paulvee/VBA-Curve-Tracer/Back Panel/BP-2DBOTRev2b.JPG

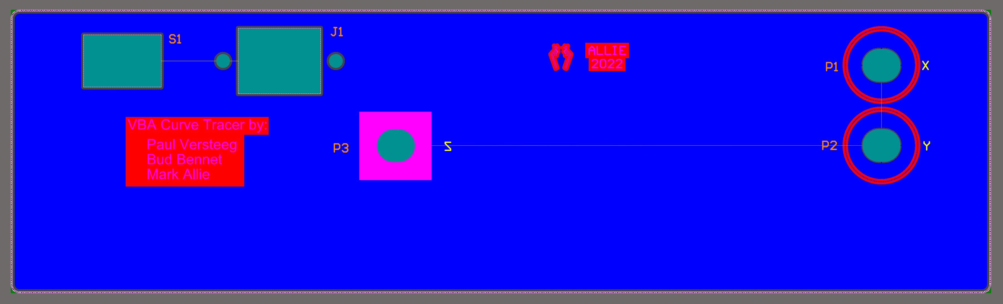
Back Panel/BP-2DBOTRev2b.JPG
