paulvee/VBA-Curve-Tracer/Back Panel/BP-2DTOPRev2b.JPG

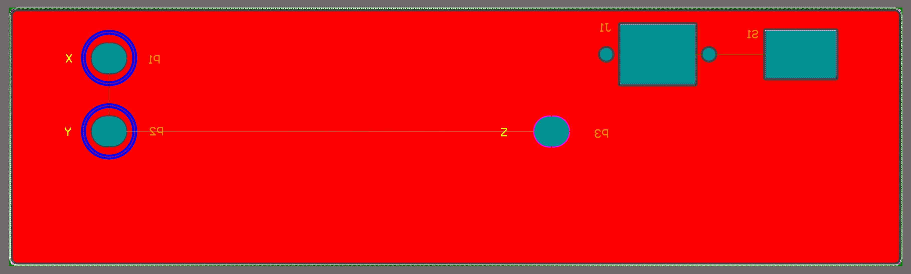
Back Panel/BP-2DTOPRev2b.JPG
