paulvee/VBA-Curve-Tracer/Back Panel/BP-3DBOTRev2b.JPG

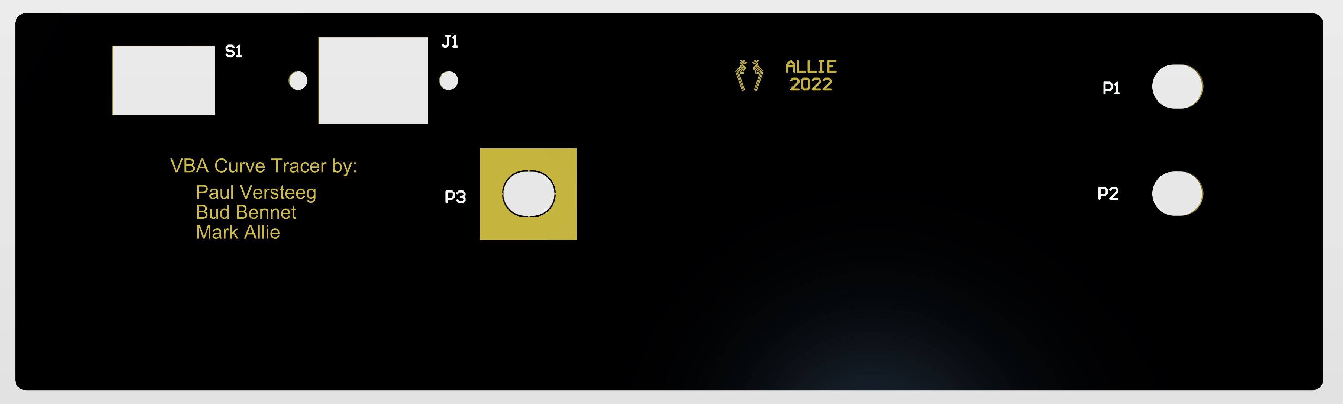
Back Panel/BP-3DBOTRev2b.JPG
