paulvee/VBA-Curve-Tracer/Back Panel/BP-3DTOPRev2b.JPG

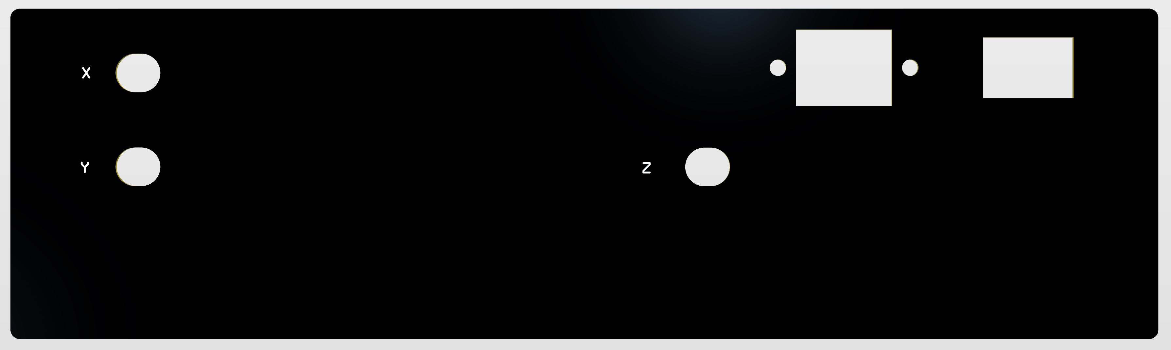
Back Panel/BP-3DTOPRev2b.JPG
