paulvee/VBA-Curve-Tracer/CT plus DSO-sm.jpg

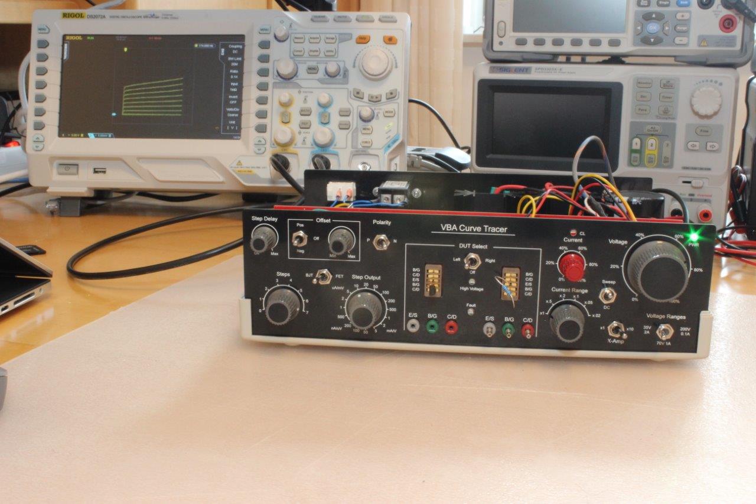
CT plus DSO-sm.jpg
