paulvee/VBA-Curve-Tracer/Front Above.jpg

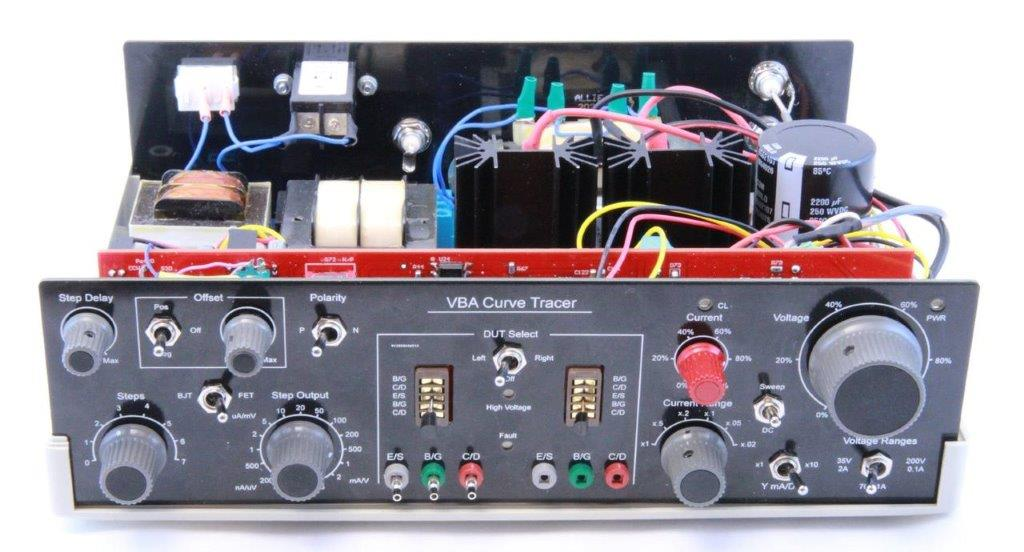
Front Above.jpg
