paulvee/VBA-Curve-Tracer/Front Board/CurrentAndVoltageSet-Rev2b.png

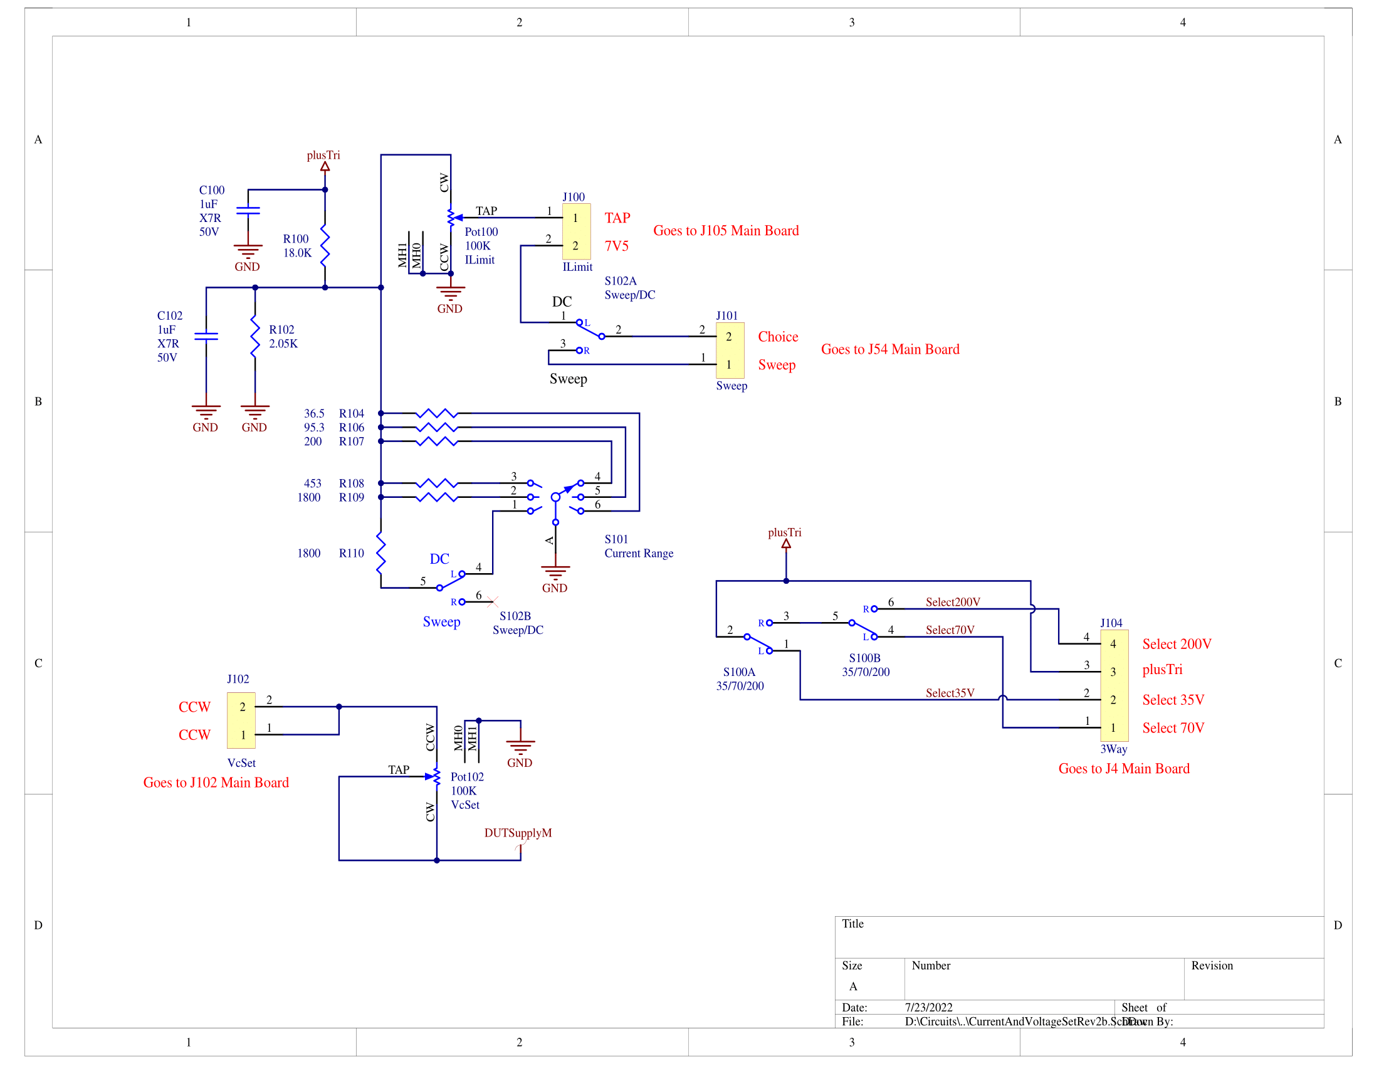
Front Board/CurrentAndVoltageSet-Rev2b.png
