paulvee/VBA-Curve-Tracer/Front Board/D2A-Rev2b.png

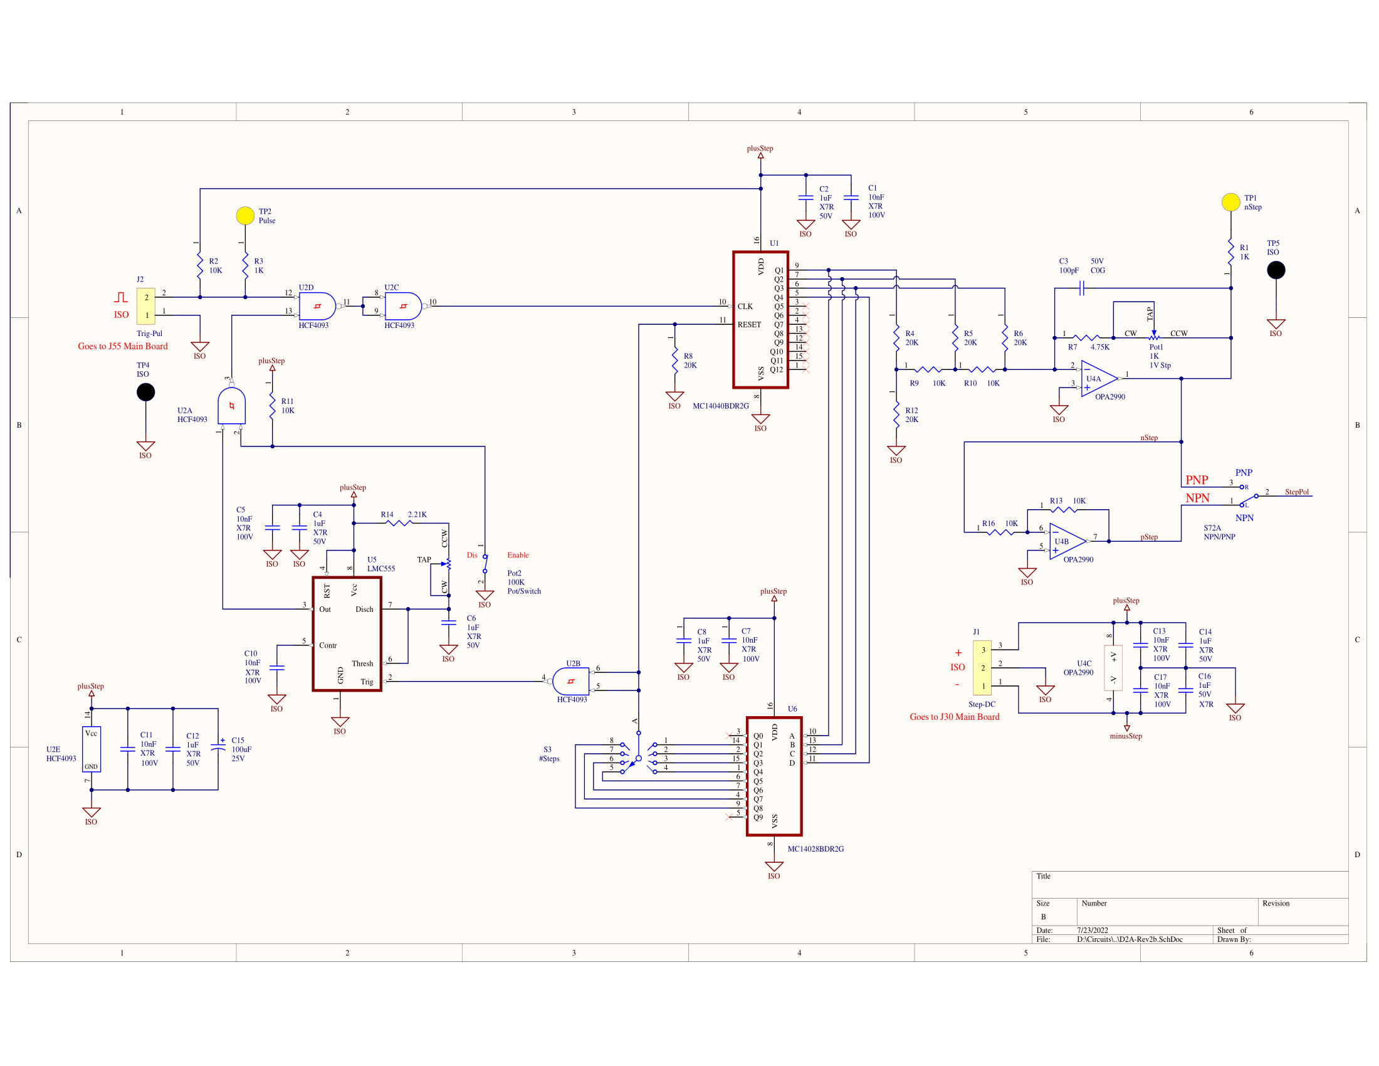
Front Board/D2A-Rev2b.png
