paulvee/VBA-Curve-Tracer/Front Board/FaultDetect-Rev2b.png

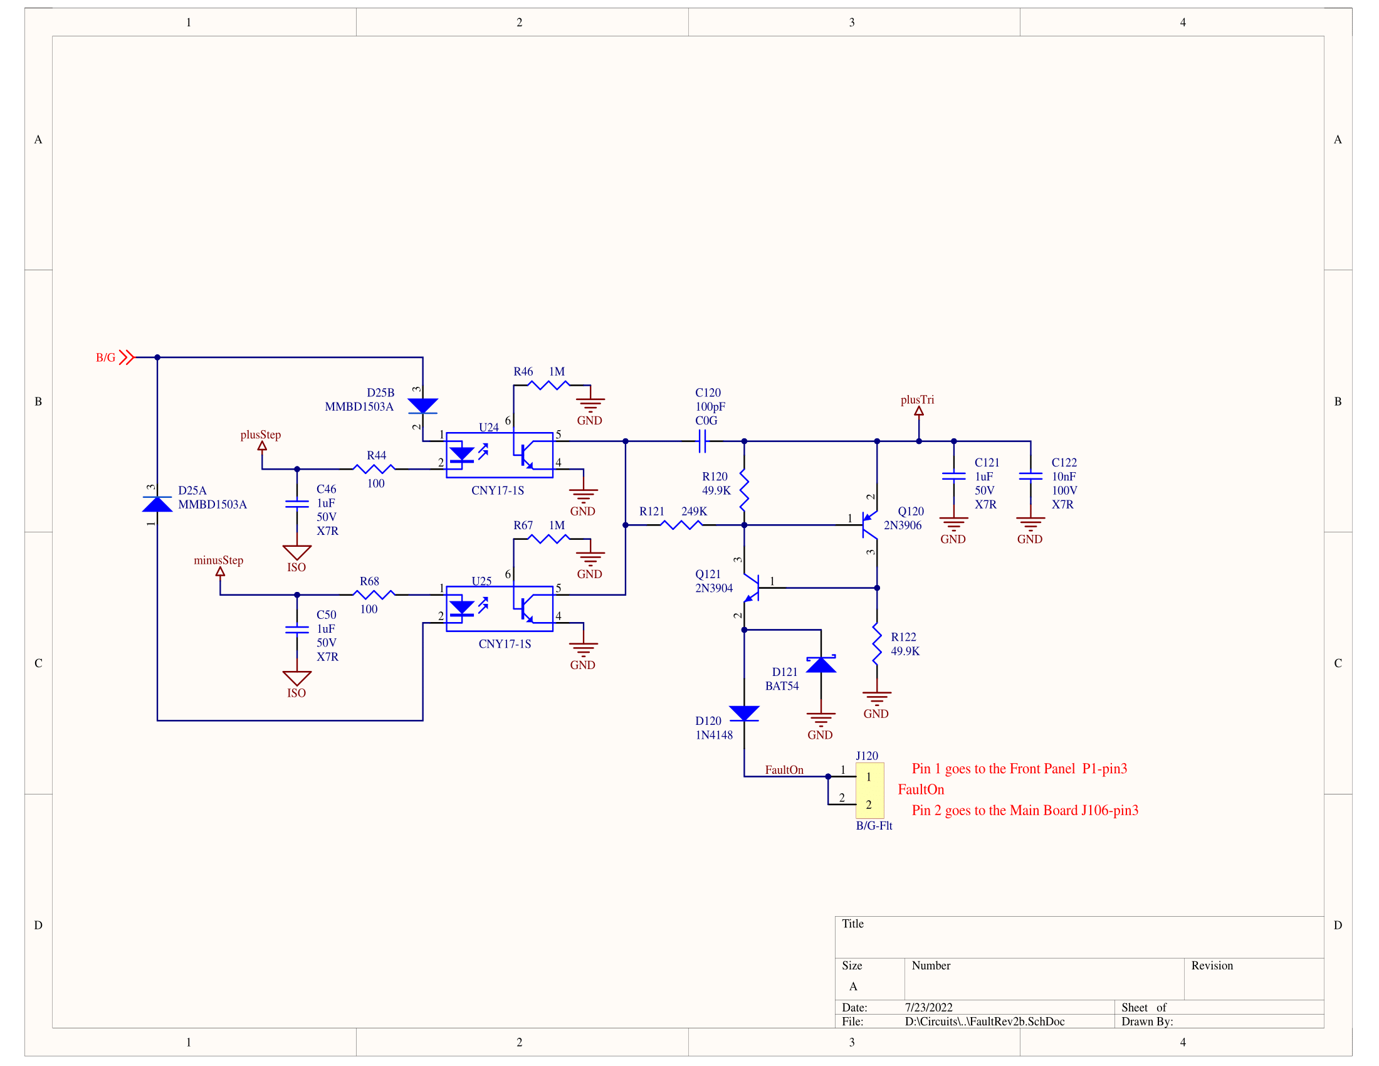
Front Board/FaultDetect-Rev2b.png
