paulvee/VBA-Curve-Tracer/Front Board/FB-2D-BOT-NoGND-NoISO-Rev2b.JPG

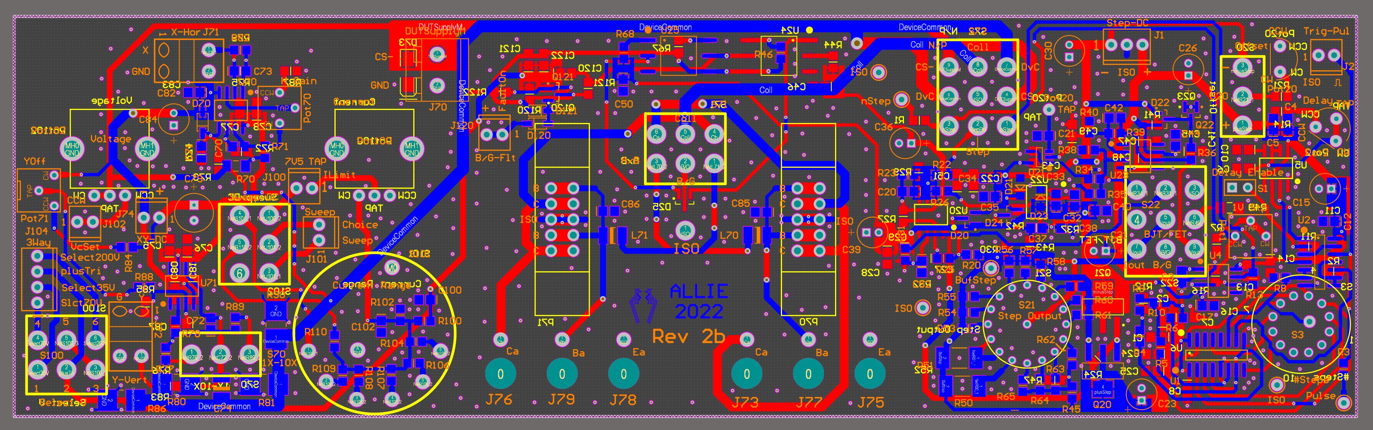
Front Board/FB-2D-BOT-NoGND-NoISO-Rev2b.JPG
