paulvee/VBA-Curve-Tracer/Front Board/FB-2D-TOP-NoGND-NoISO-Rev2b.JPG

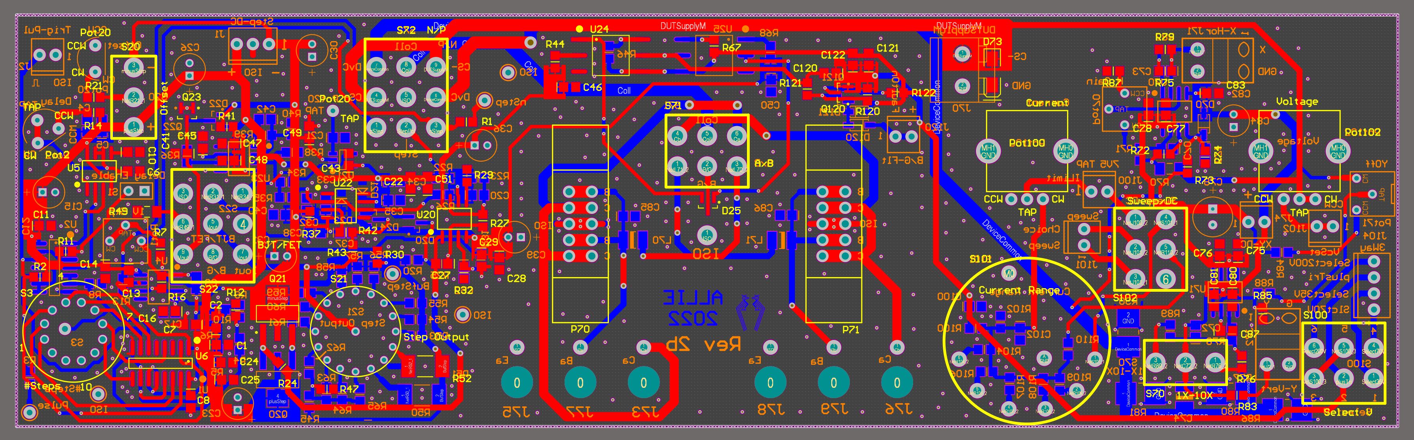
Front Board/FB-2D-TOP-NoGND-NoISO-Rev2b.JPG
