paulvee/VBA-Curve-Tracer/Front Board/FB-3D-BOT-Rev2b.png

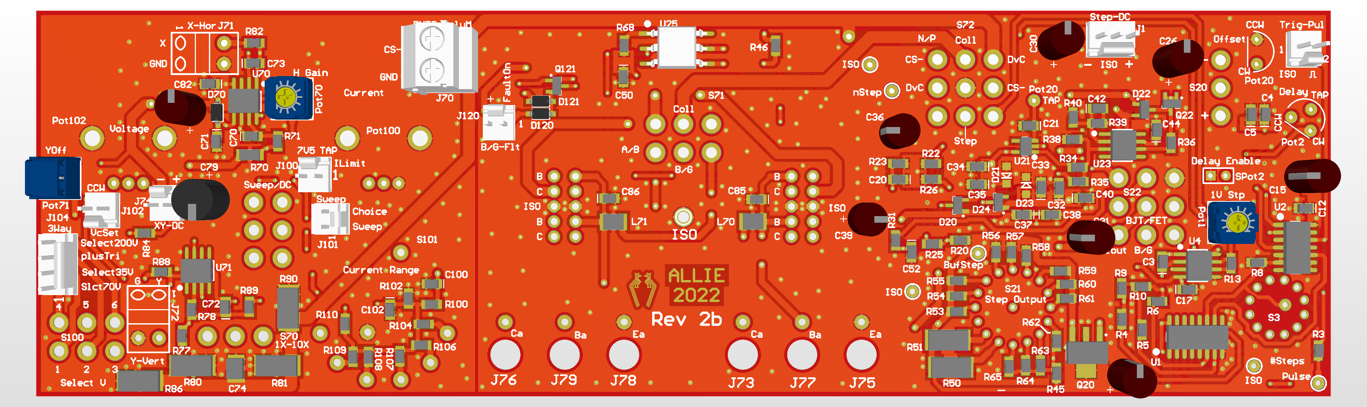
Front Board/FB-3D-BOT-Rev2b.png
