paulvee/VBA-Curve-Tracer/Front Board/FB-3D-TOP-Rev2b.png

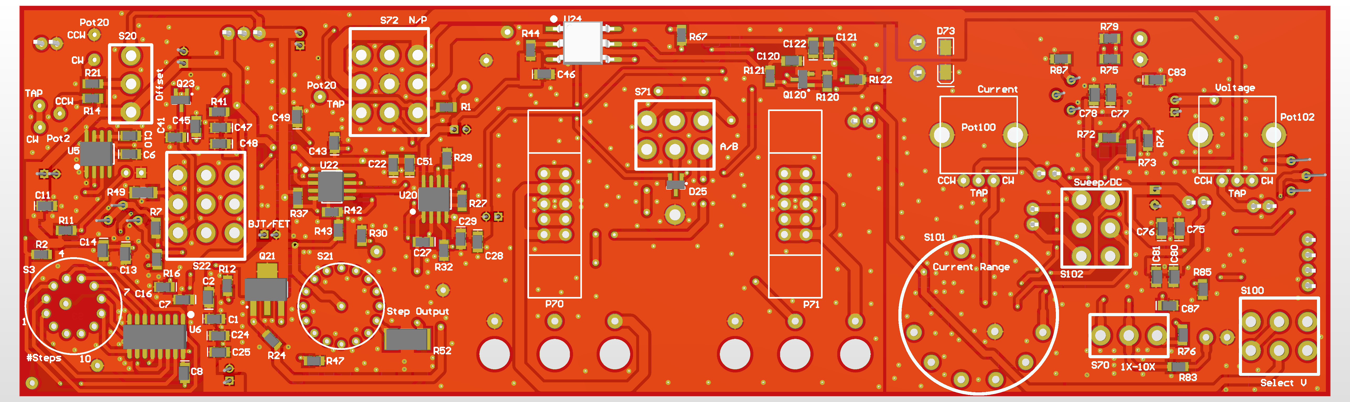
Front Board/FB-3D-TOP-Rev2b.png
