paulvee/VBA-Curve-Tracer/Front Board/XYAmp-Rev2b.png

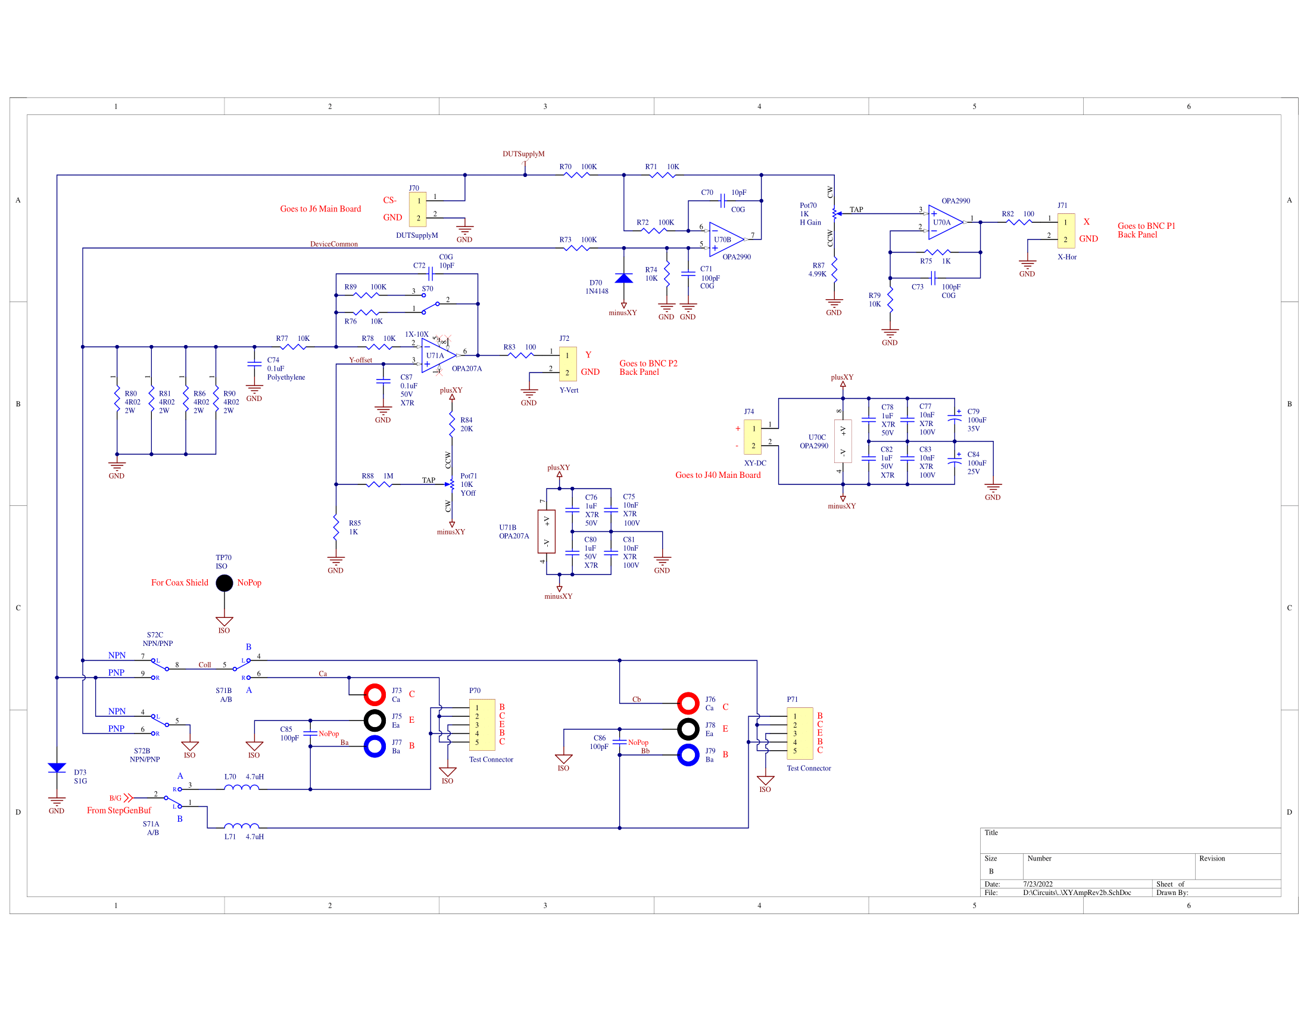
Front Board/XYAmp-Rev2b.png
