paulvee/VBA-Curve-Tracer/Front Panel/CT_Boxed(small).jpg

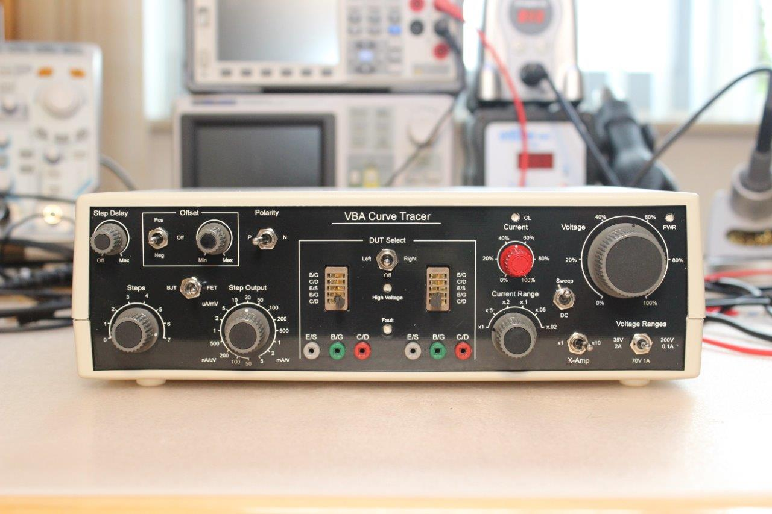
Front Panel/CT_Boxed(small).jpg
