paulvee/VBA-Curve-Tracer/Front Panel/FP-2D-BOT-Rev2b.png

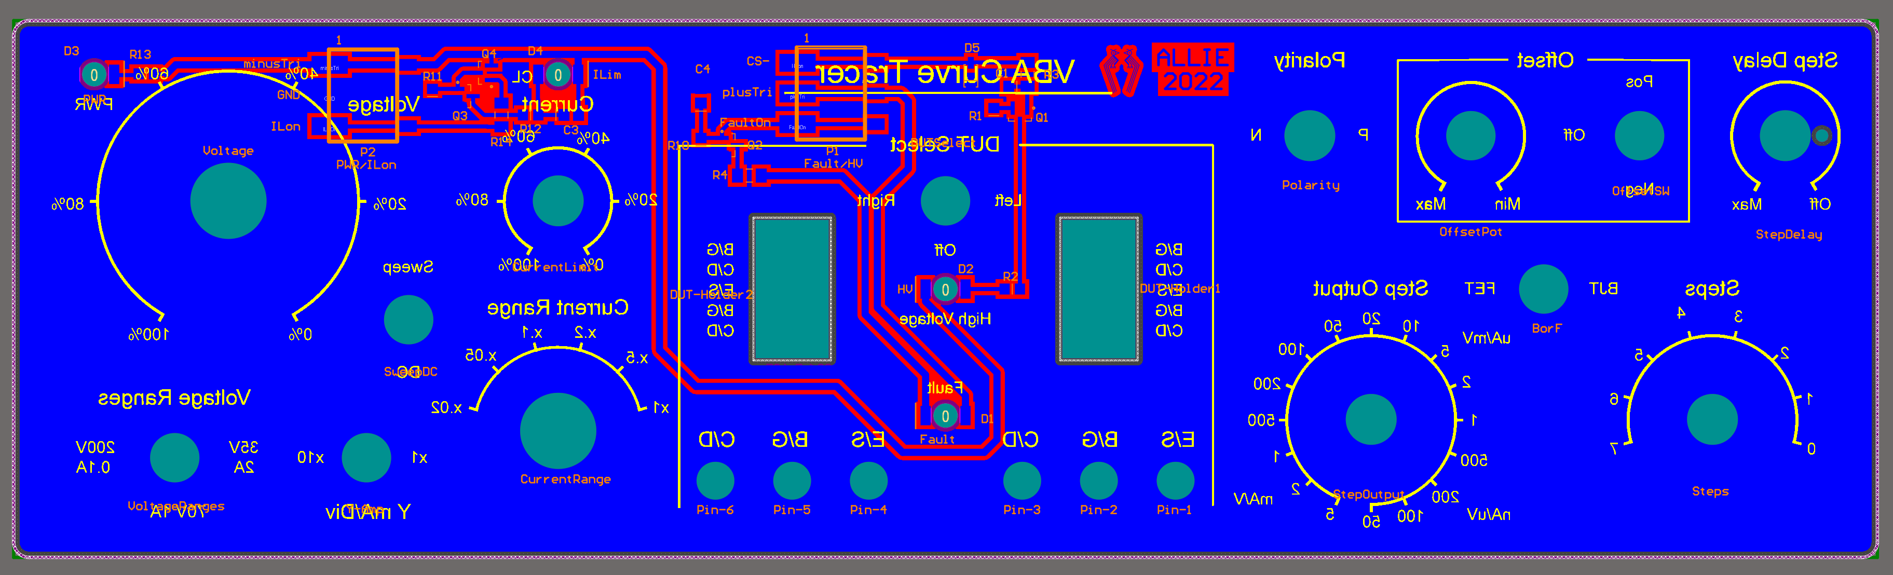
Front Panel/FP-2D-BOT-Rev2b.png
