paulvee/VBA-Curve-Tracer/Front Panel/FP-2D-TOP-Rev2b.png

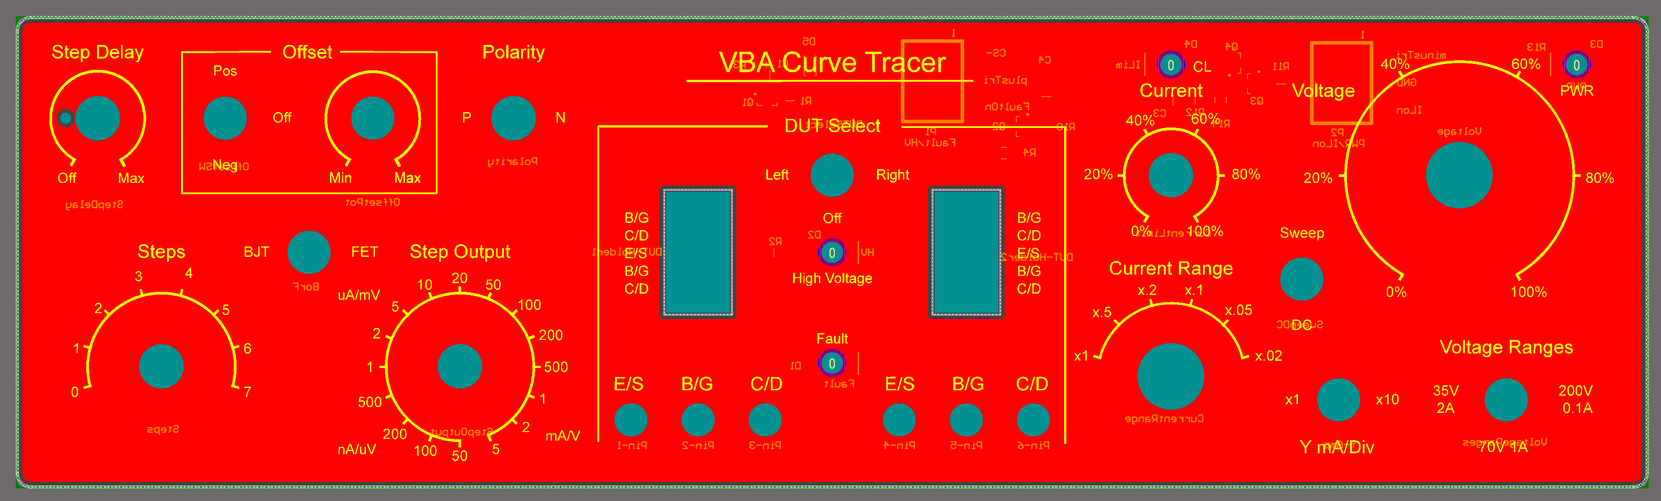
Front Panel/FP-2D-TOP-Rev2b.png
