paulvee/VBA-Curve-Tracer/Front Panel/FP-3D-BOT-Rev2b.png

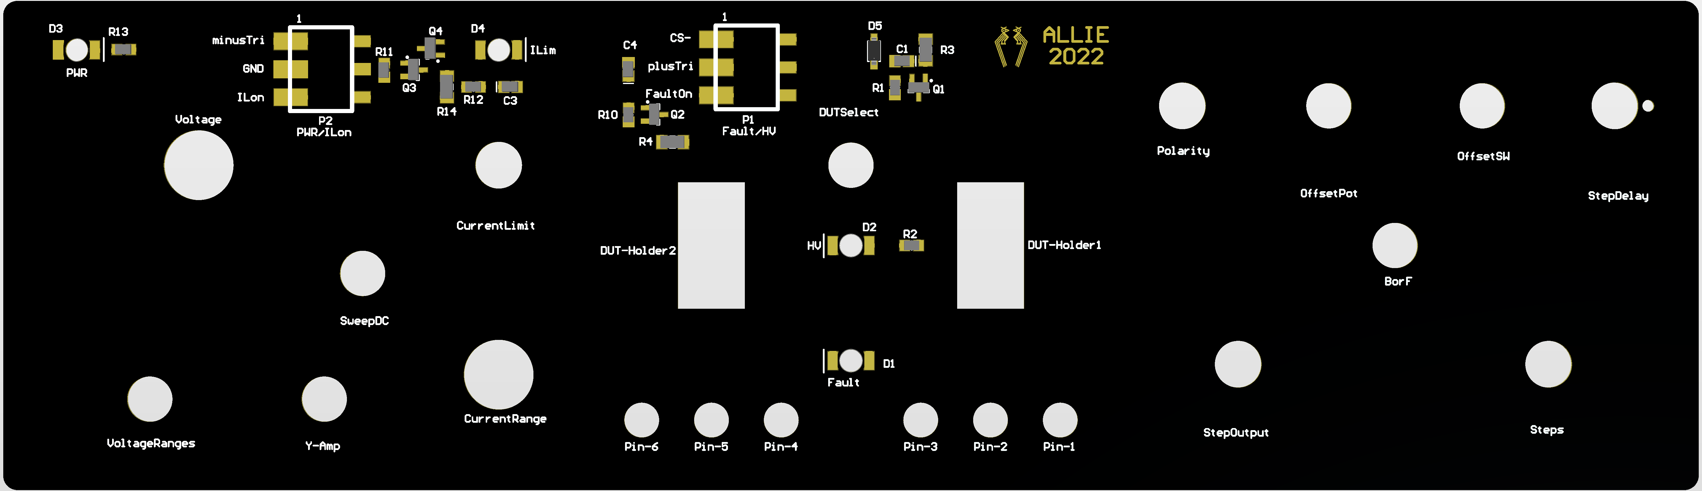
Front Panel/FP-3D-BOT-Rev2b.png
