paulvee/VBA-Curve-Tracer/Front Panel/FP-3D-TOP-Rev2b.png

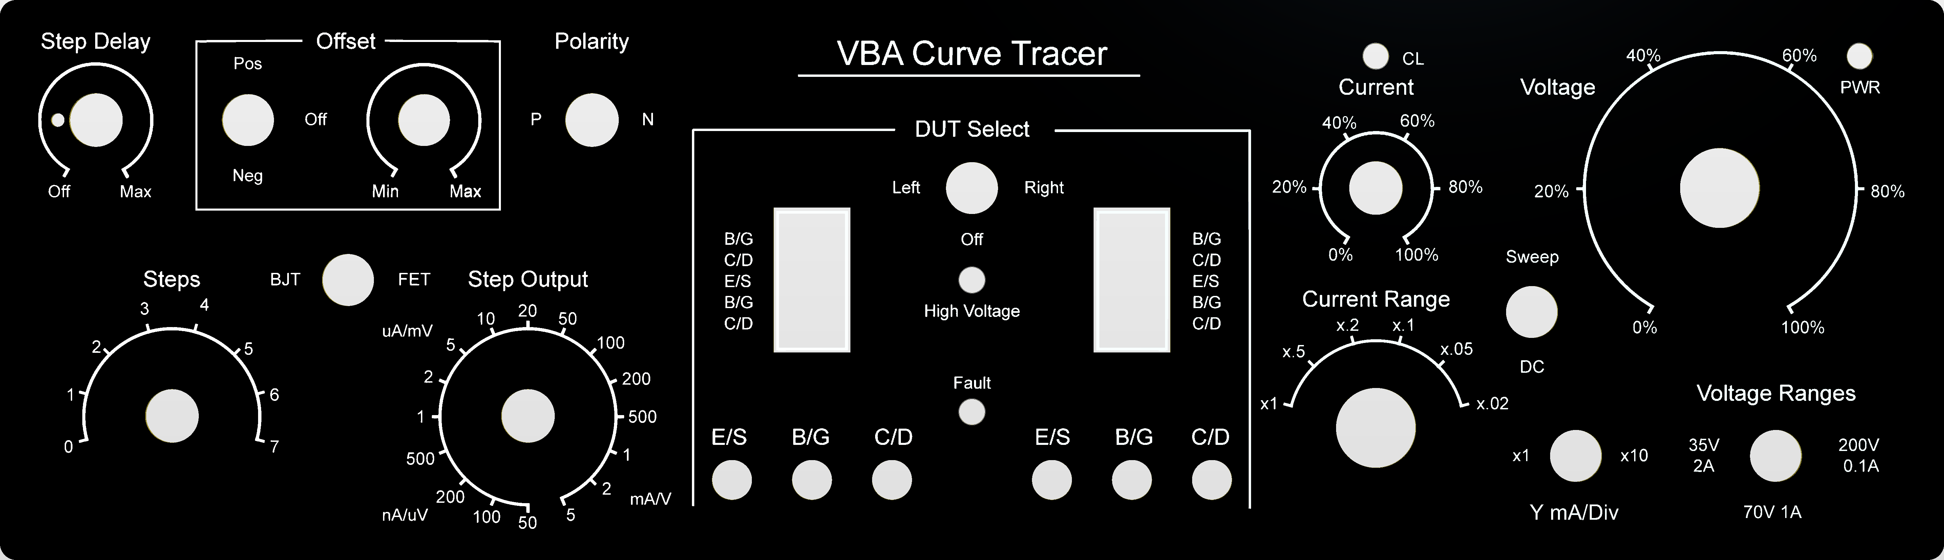
Front Panel/FP-3D-TOP-Rev2b.png
