paulvee/VBA-Curve-Tracer/Front Panel/FrontPanel-Rev2b.png

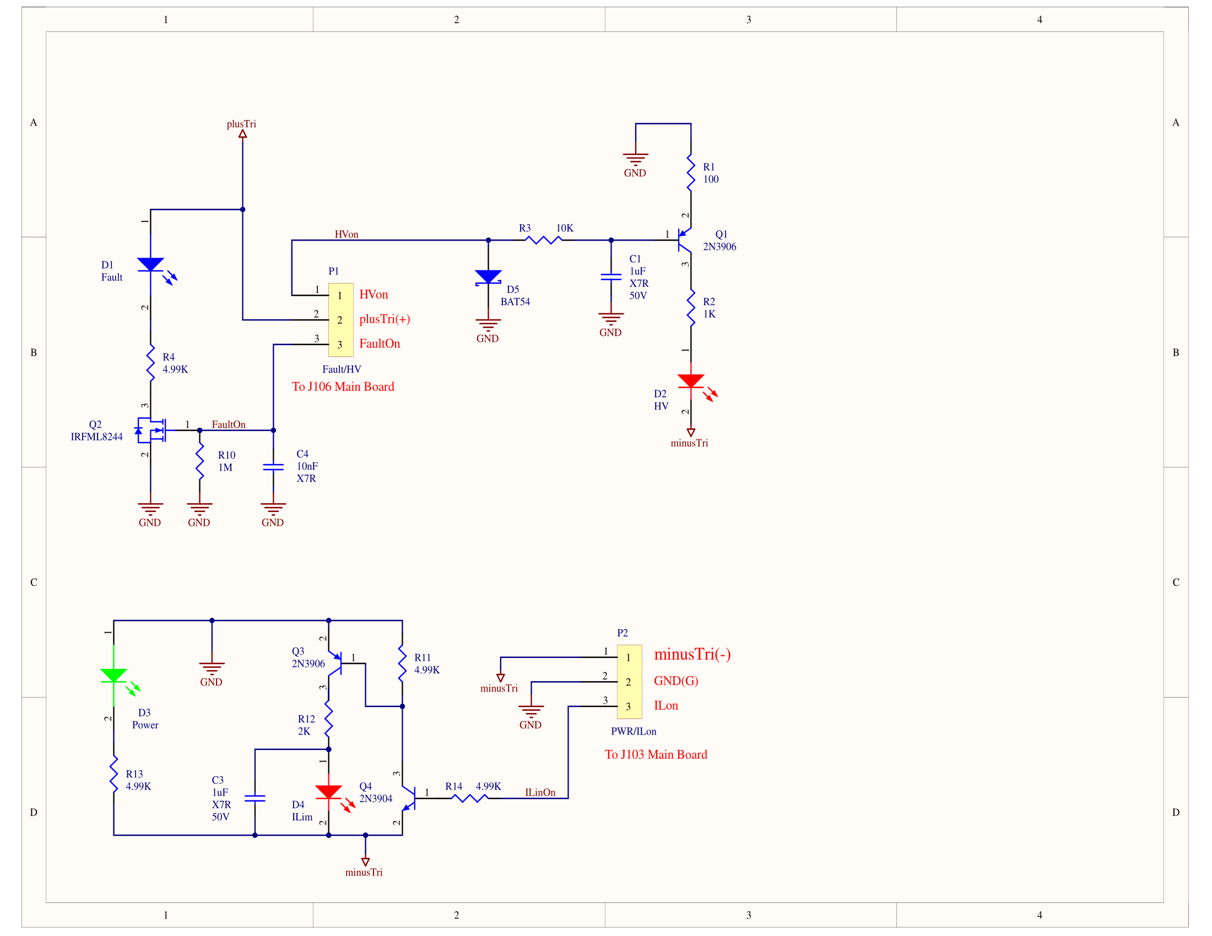
Front Panel/FrontPanel-Rev2b.png
