paulvee/VBA-Curve-Tracer/Front Panel/MountingHoles-Rev2b.png

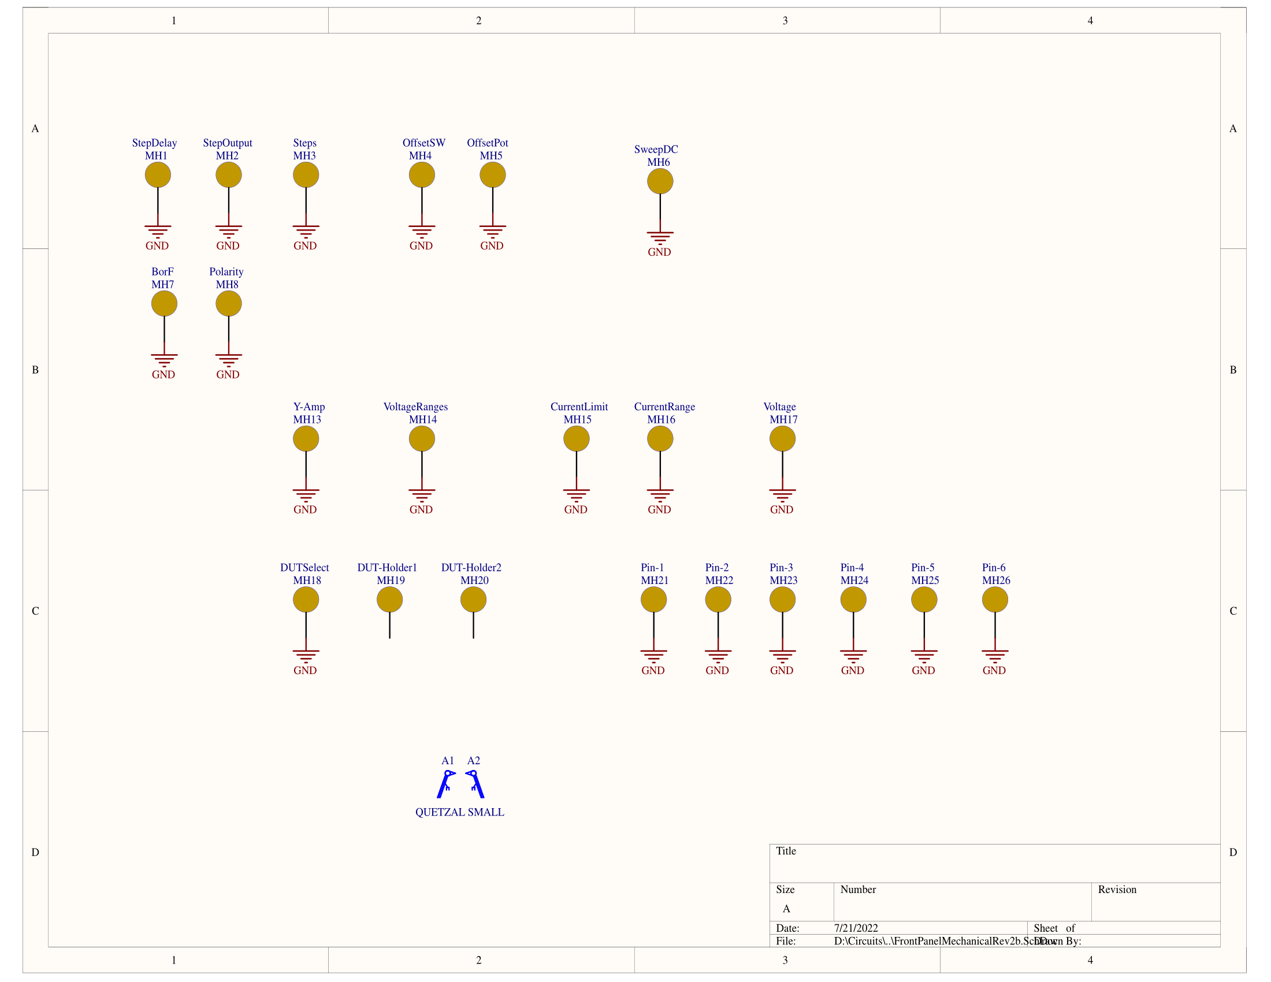
Front Panel/MountingHoles-Rev2b.png
