paulvee/VBA-Curve-Tracer/Front Panel/VBA-CT-Mark.jpg

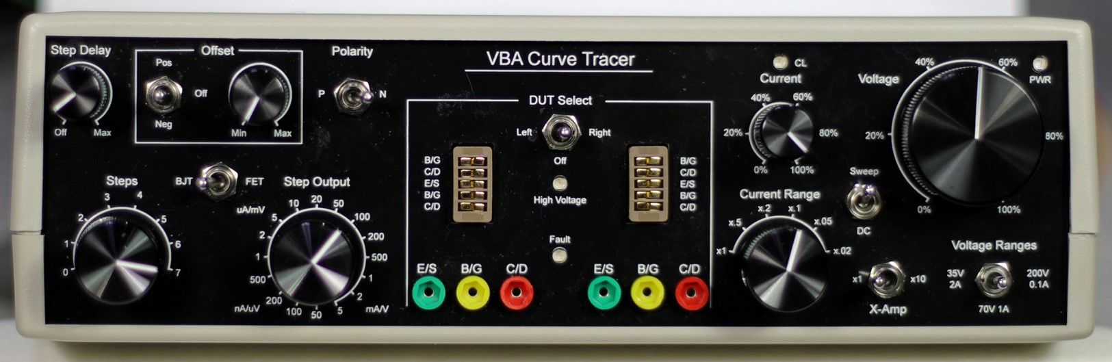
Front Panel/VBA-CT-Mark.jpg
