paulvee/VBA-Curve-Tracer/Main Board/ACSupply-Rev2b.png

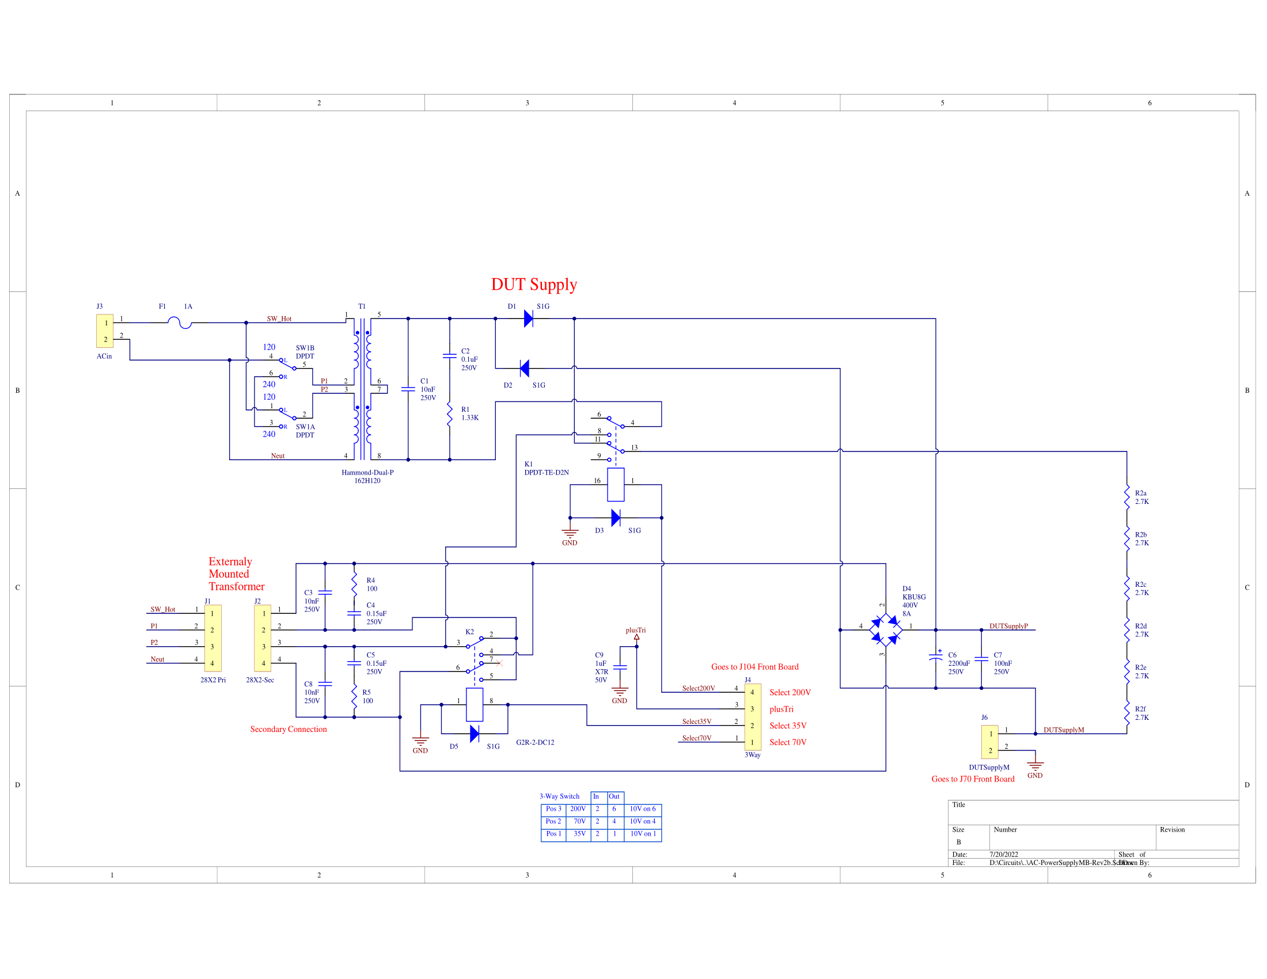
Main Board/ACSupply-Rev2b.png
