paulvee/VBA-Curve-Tracer/Main Board/CurrentSource-Rev2b.png

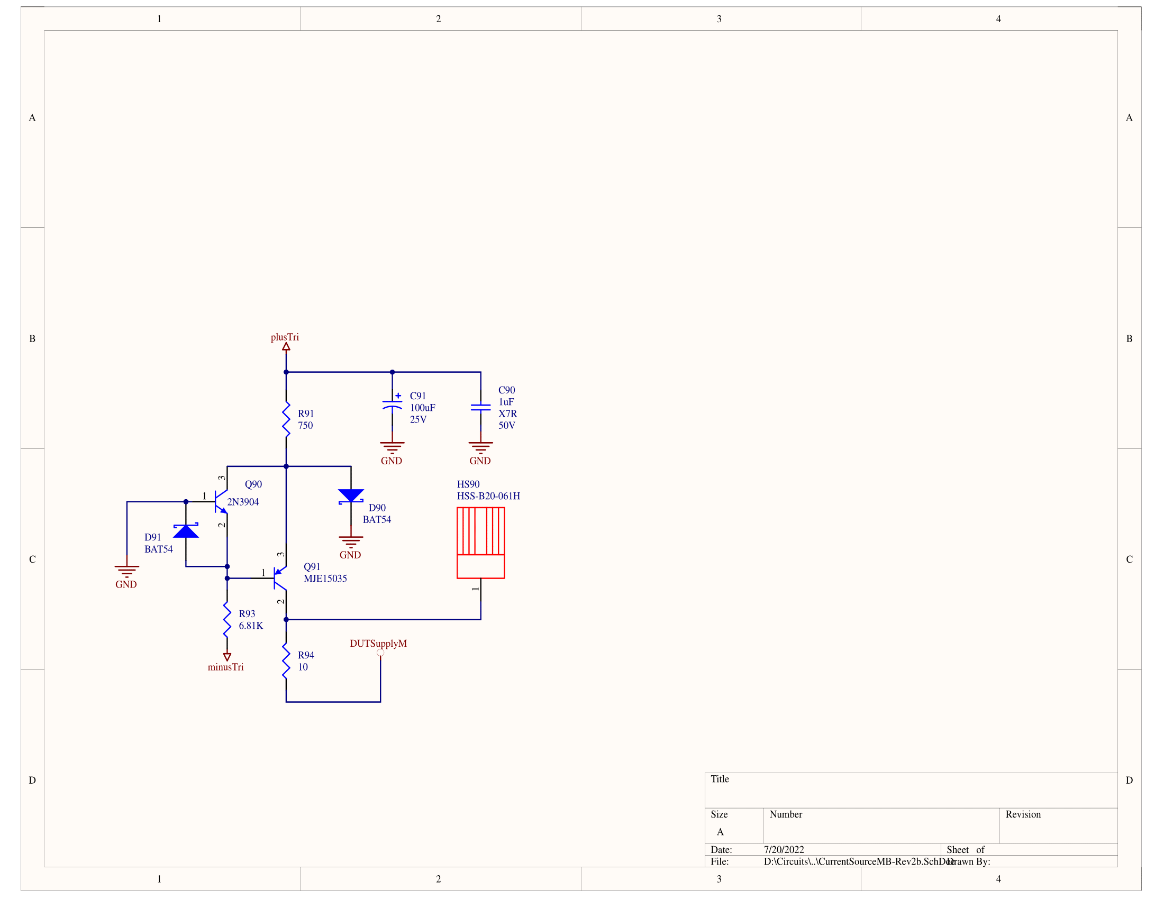
Main Board/CurrentSource-Rev2b.png
