paulvee/VBA-Curve-Tracer/Main Board/DUTSupply-Rev2b.png

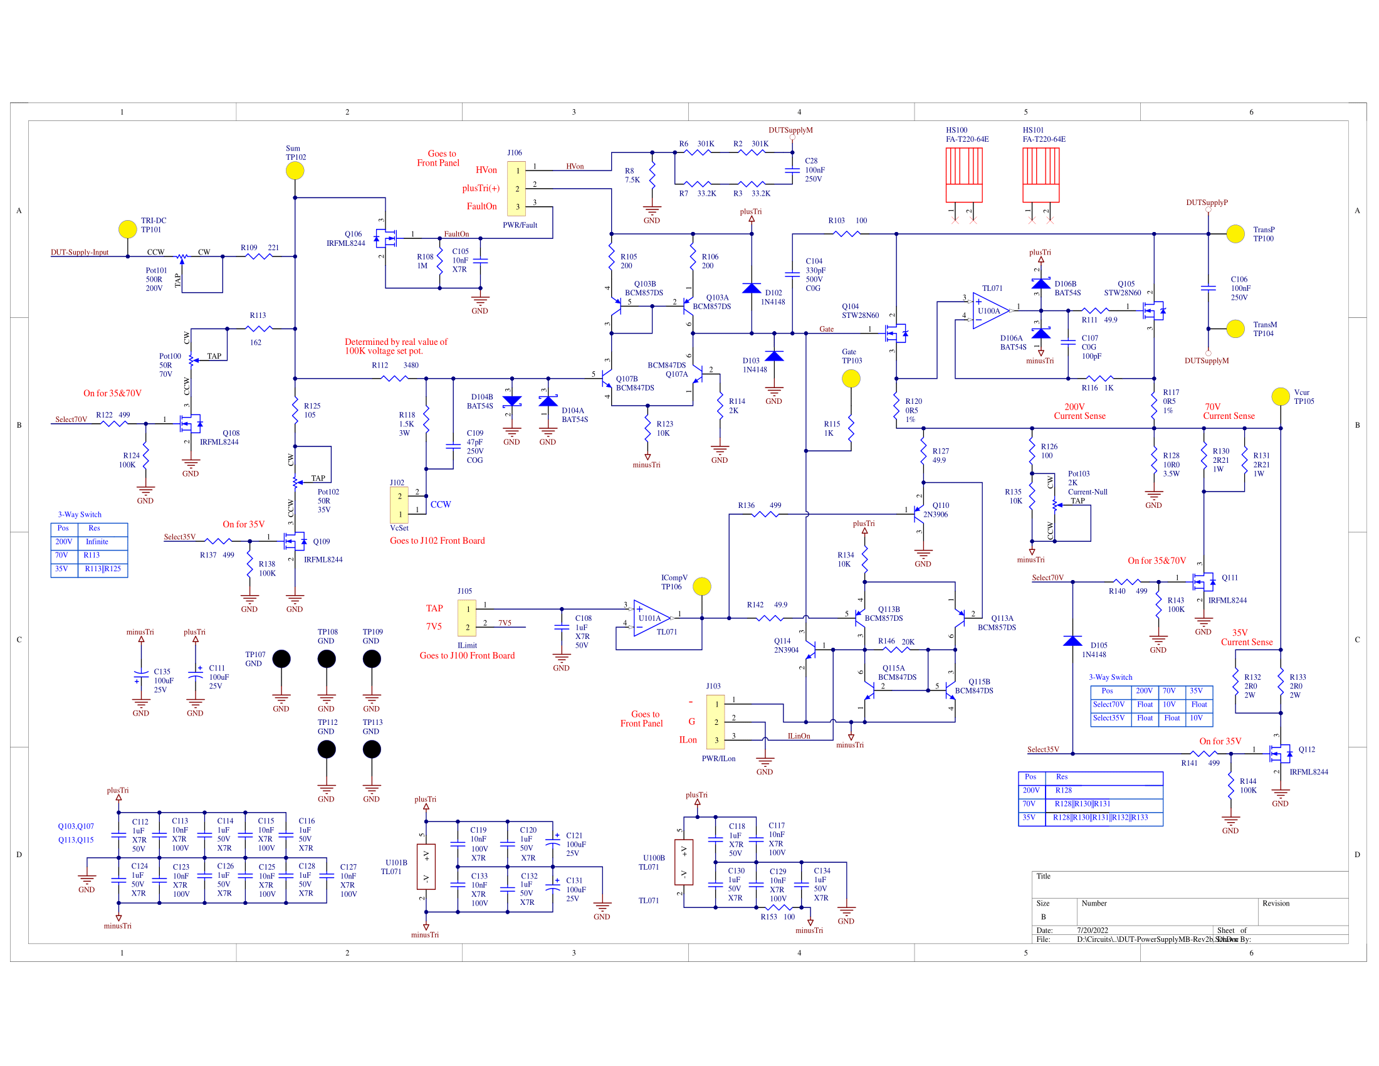
Main Board/DUTSupply-Rev2b.png
