paulvee/VBA-Curve-Tracer/Main Board/IsolatedSupply-Rev2b.png

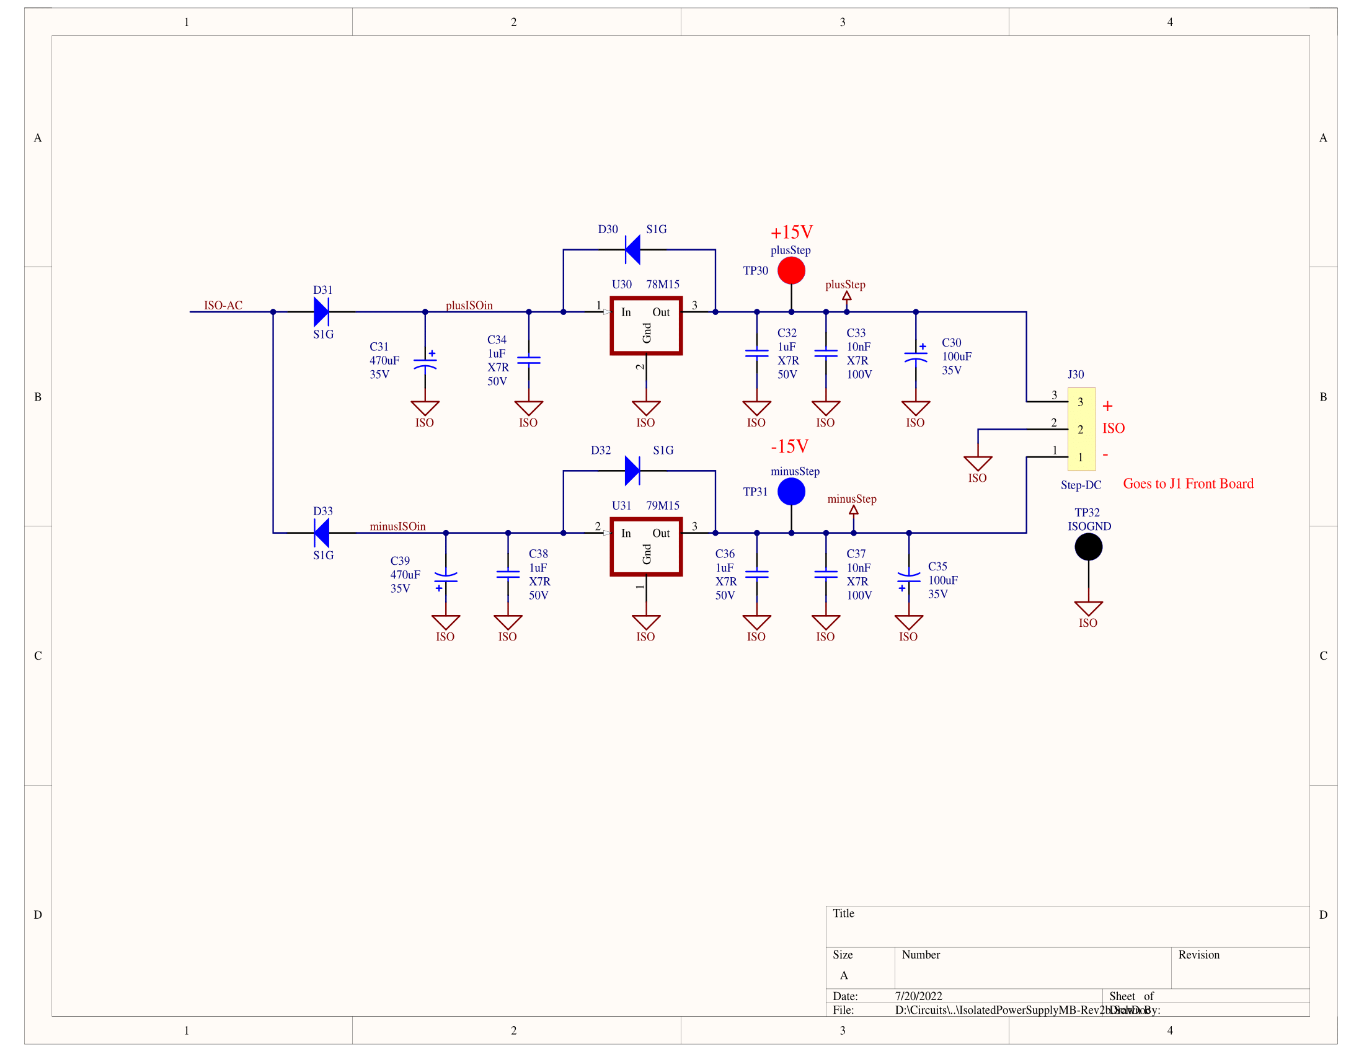
Main Board/IsolatedSupply-Rev2b.png
