paulvee/VBA-Curve-Tracer/Main Board/MB-2D-NoGND-BOTRev2b.JPG

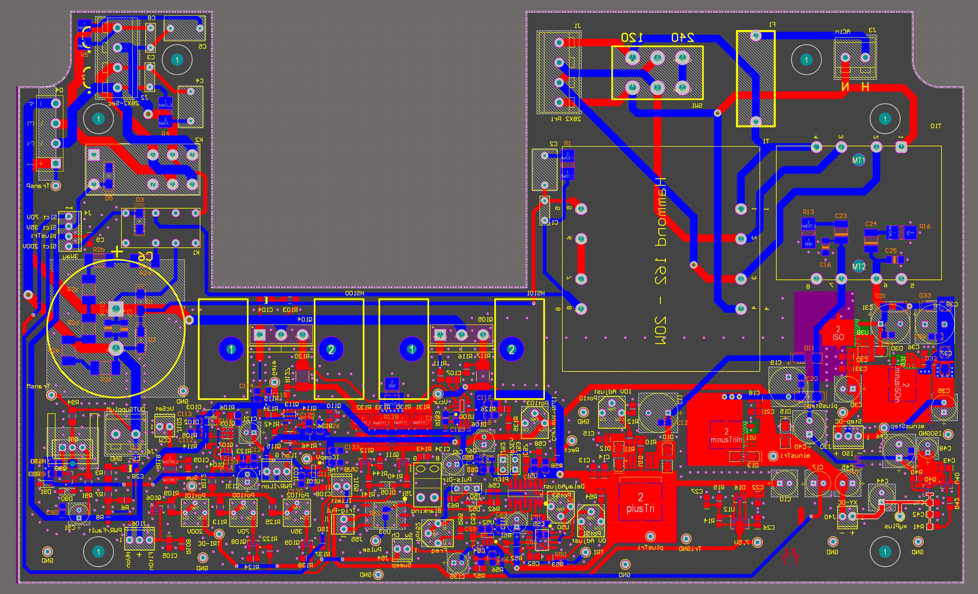
Main Board/MB-2D-NoGND-BOTRev2b.JPG
