paulvee/VBA-Curve-Tracer/Main Board/MB-2D-NoGND-TOPRev2b.JPG

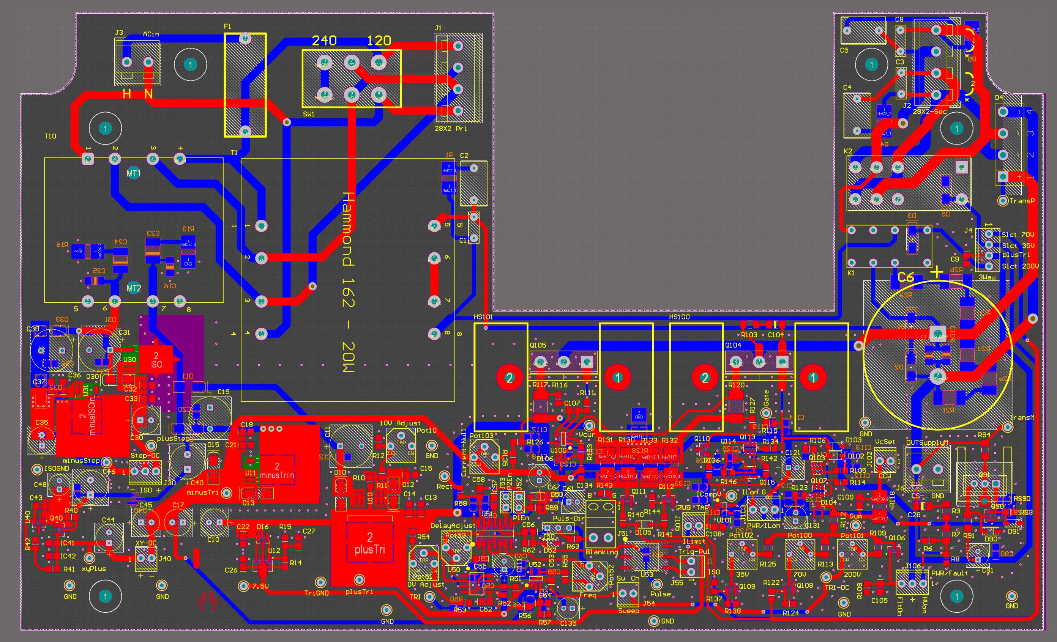
Main Board/MB-2D-NoGND-TOPRev2b.JPG
