paulvee/VBA-Curve-Tracer/Main Board/MB-3DBOTRev2b.png

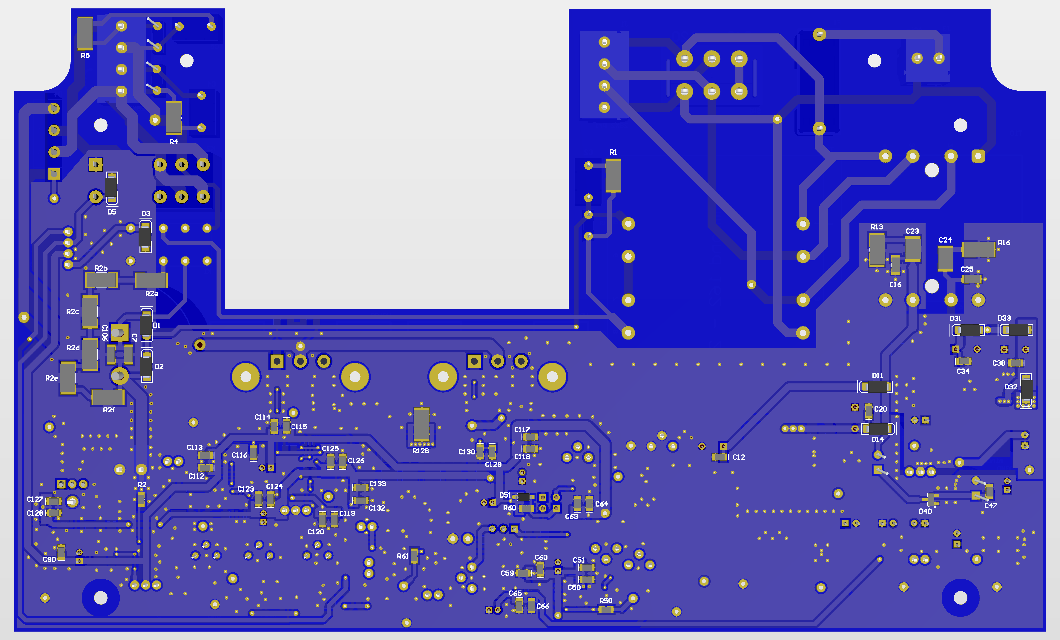
Main Board/MB-3DBOTRev2b.png
