paulvee/VBA-Curve-Tracer/Main Board/MB-3DTOPRev2b.png

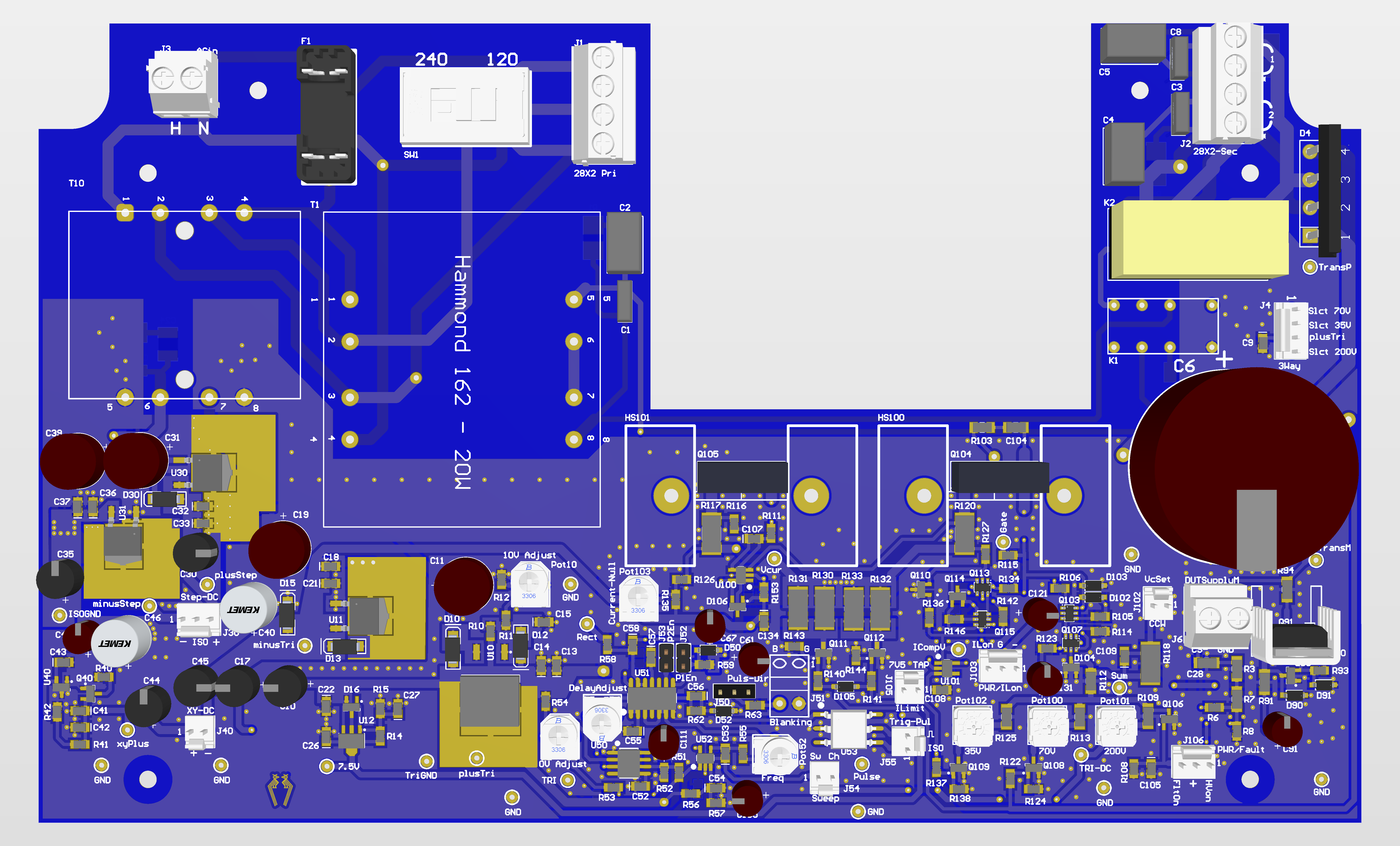
Main Board/MB-3DTOPRev2b.png
