paulvee/VBA-Curve-Tracer/Main Board/MountingHoles-Rev2b.png

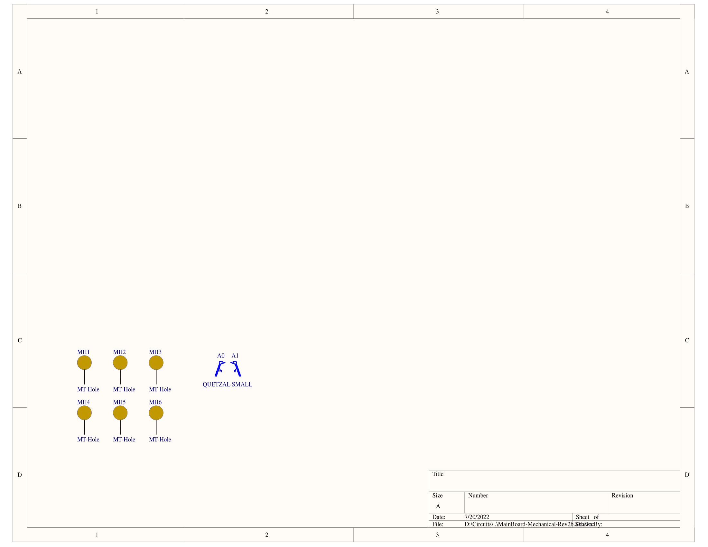
Main Board/MountingHoles-Rev2b.png
