paulvee/VBA-Curve-Tracer/Main Board/TriangleGenerator-Rev2b.png

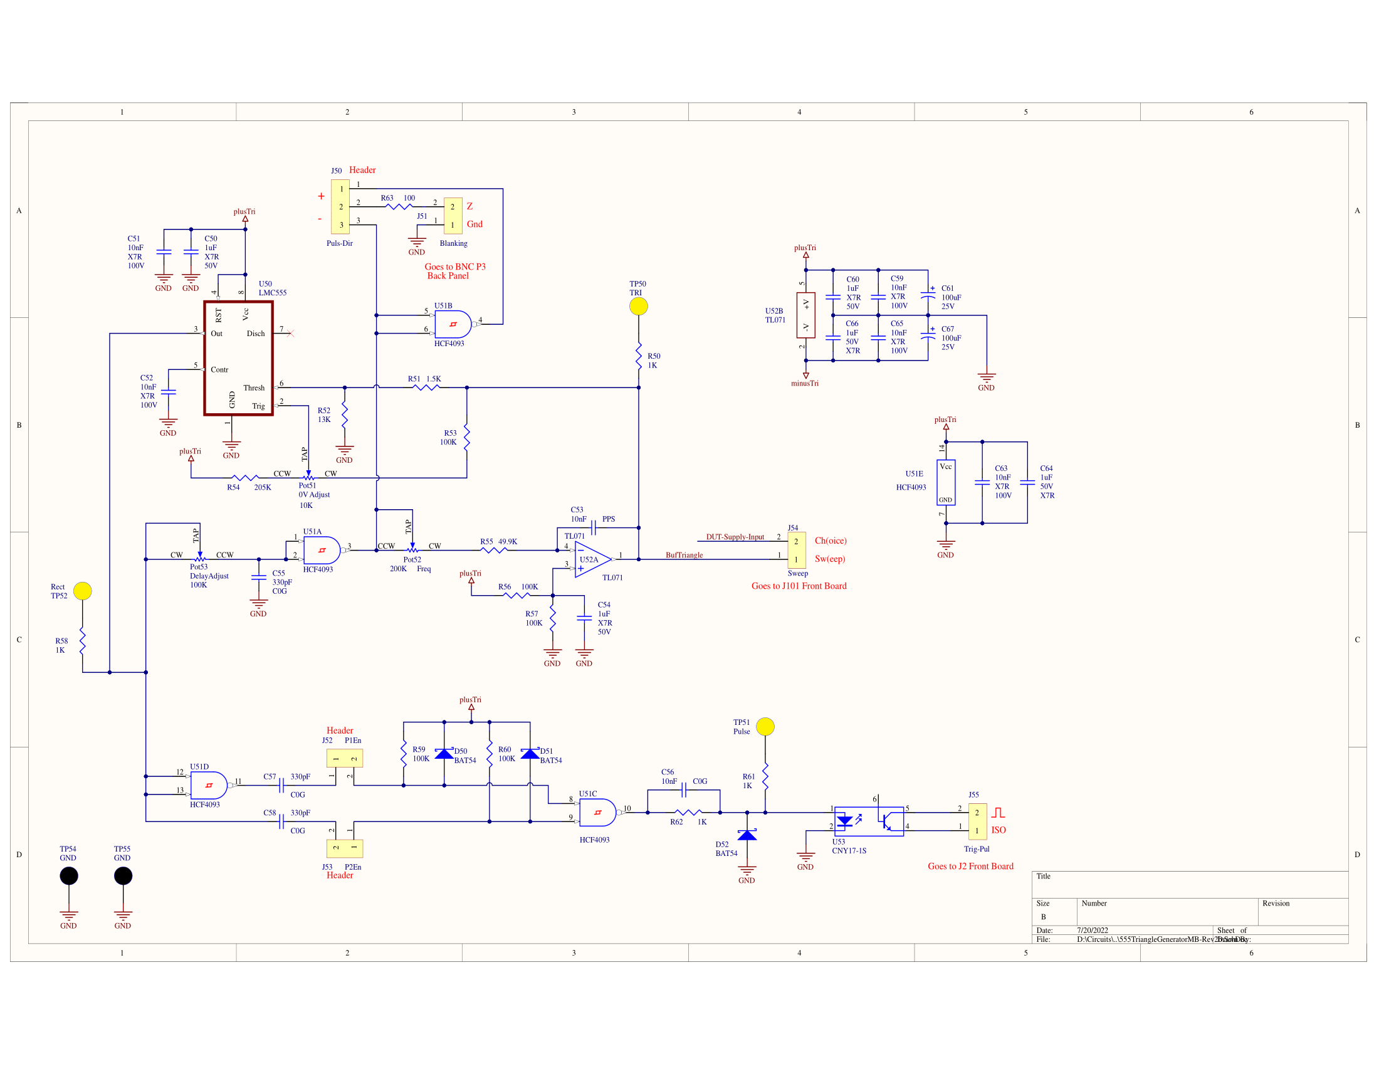
Main Board/TriangleGenerator-Rev2b.png
