paulvee/VBA-Curve-Tracer/Main Board/TriangleSupply-Rev2b.png

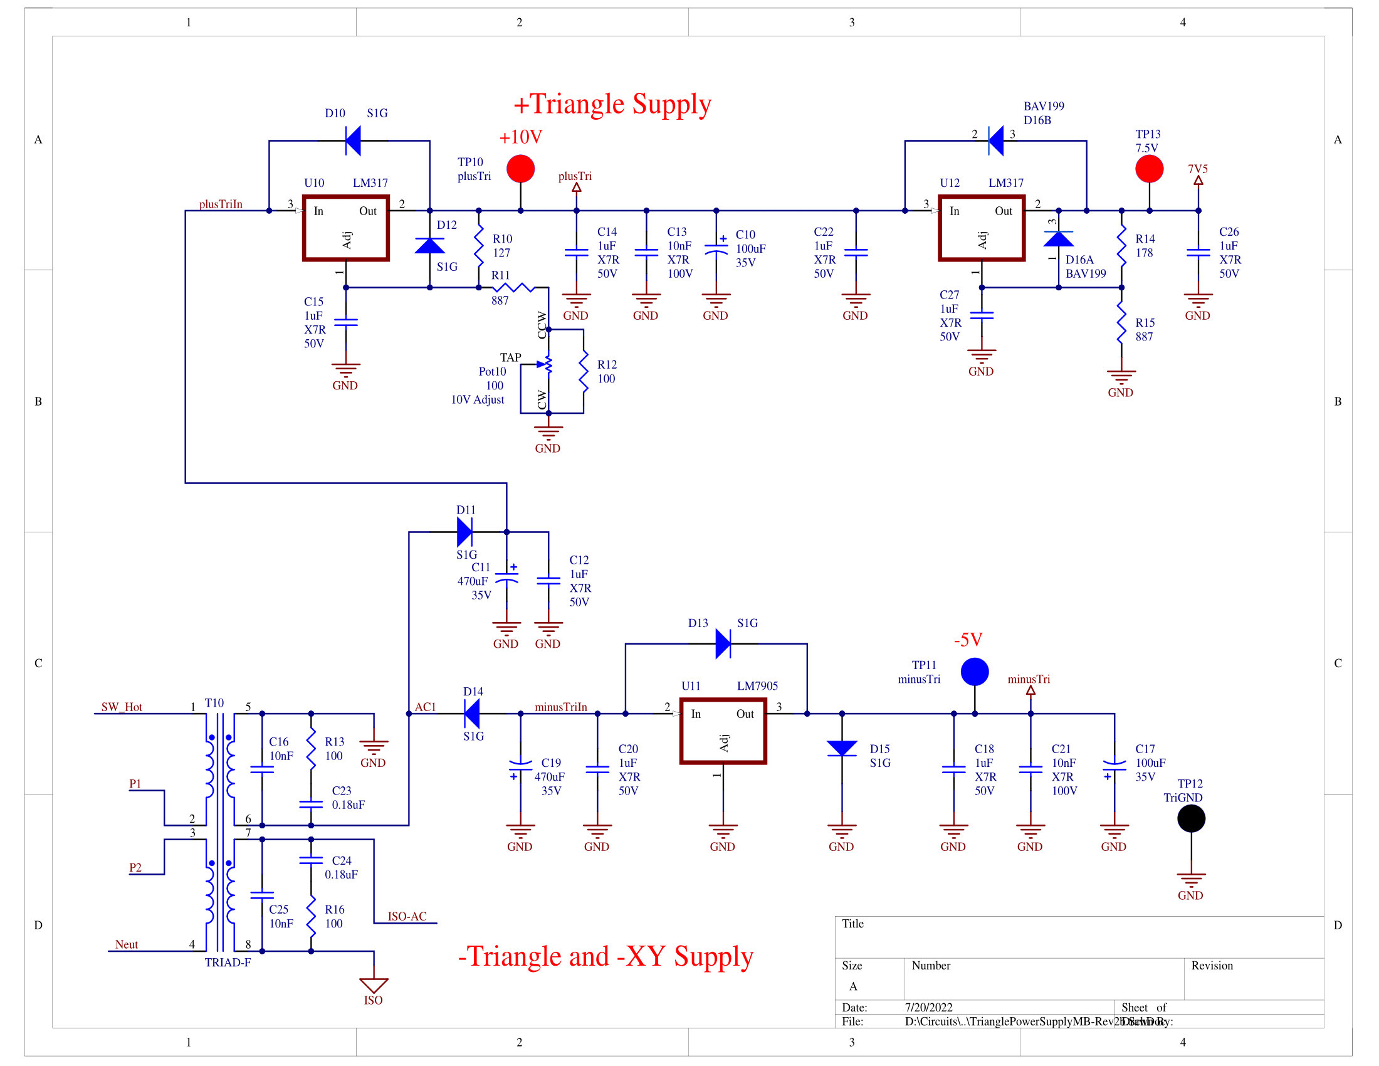
Main Board/TriangleSupply-Rev2b.png
