paulvee/VBA-Curve-Tracer/Main Board/XYSupply-Rev2b.png

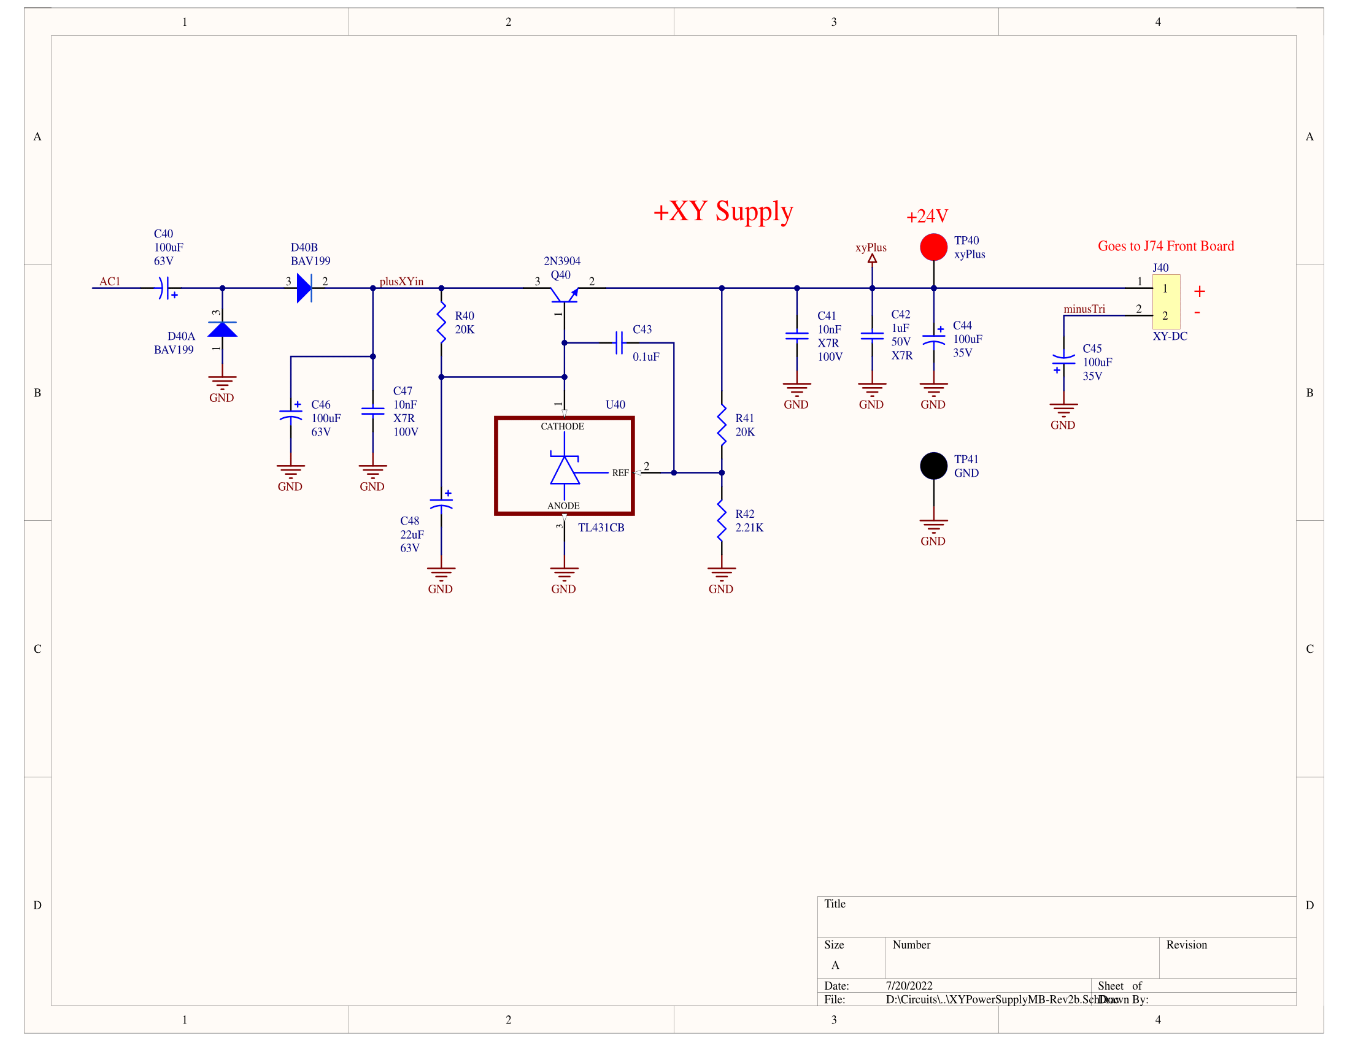
Main Board/XYSupply-Rev2b.png
