paulvee/VBA-Curve-Tracer/Front Board/StepGenBuffer-Rev2b.png

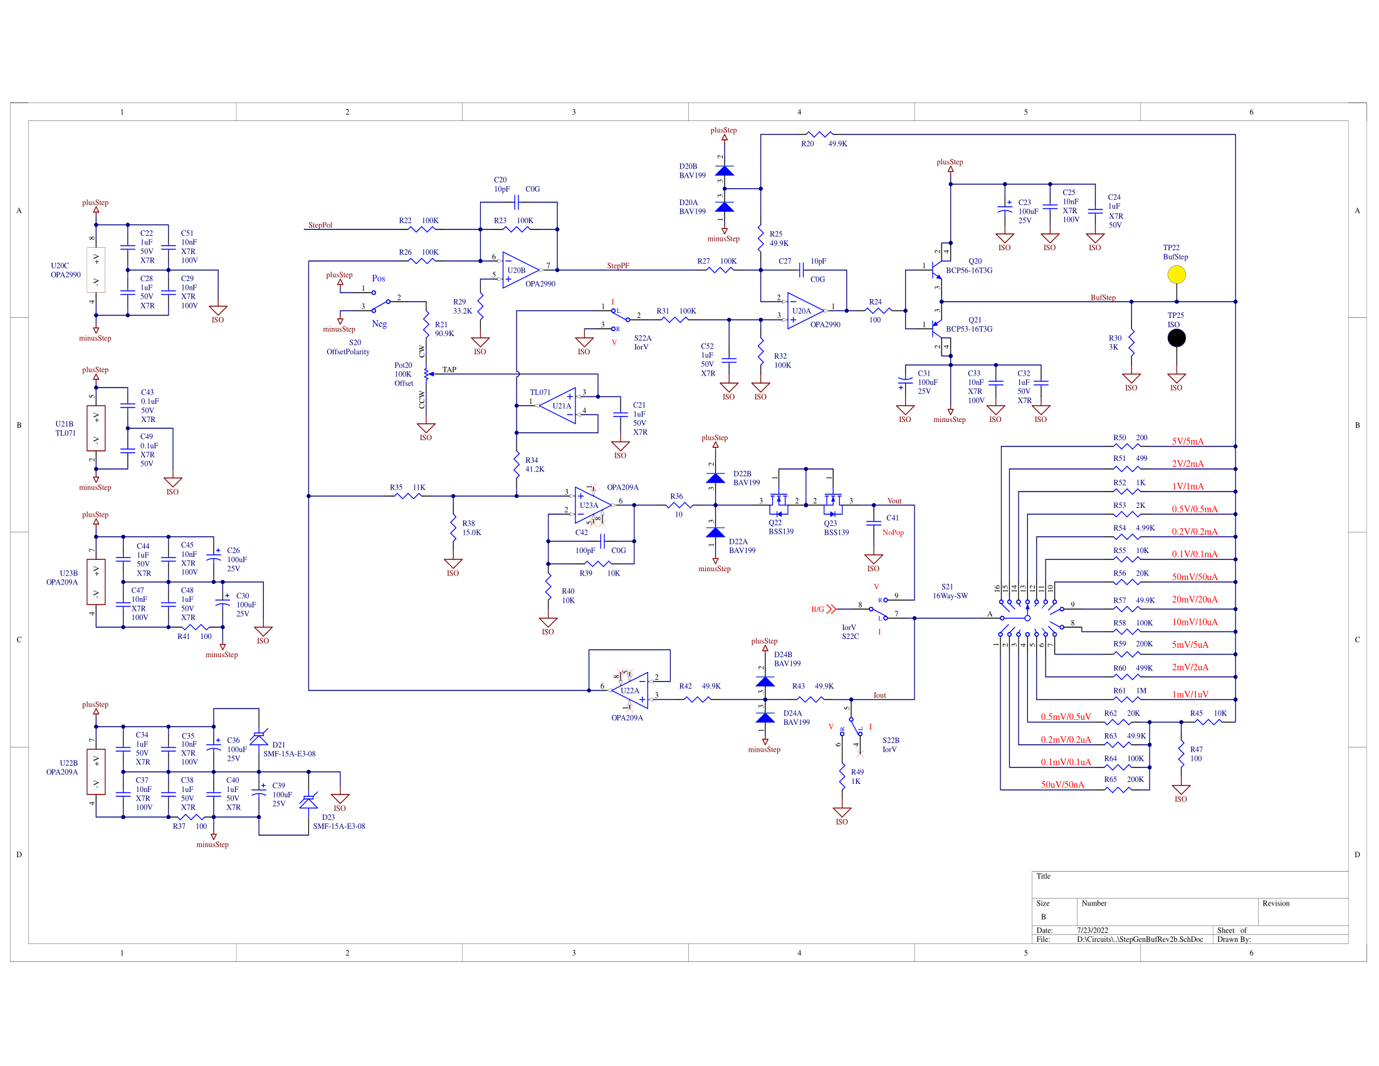
Front Board/StepGenBuffer-Rev2b.png
